7134956/nand_programmer/firmware/programmer/cdc.c

/*  Copyright (C) 2020 NANDO authors
 *  This program is free software; you can redistribute it and/or modify
 *  it under the terms of the GNU General Public License version 3.
 */

#include "ch32v30x.h"
#include "nand_programmer.h"

#define SEND_TIMEOUT 0x1000000
#include "usbd_core.h"
#include "usbd_cdc.h"

/*!< endpoint address */
#define CDC_IN_EP  0x81
#define CDC_OUT_EP 0x02
#define CDC_INT_EP 0x83

#define USBD_VID           0xFFFF
#define USBD_PID           0xFFFF
#define USBD_MAX_POWER     100
#define USBD_LANGID_STRING 1033

/*!< config descriptor size */
#define USB_CONFIG_SIZE (9 + CDC_ACM_DESCRIPTOR_LEN)

/*!< global descriptor */
static const uint8_t cdc_descriptor[] = {
    USB_DEVICE_DESCRIPTOR_INIT(USB_2_0, 0xEF, 0x02, 0x01, USBD_VID, USBD_PID, 0x0100, 0x01),
    USB_CONFIG_DESCRIPTOR_INIT(USB_CONFIG_SIZE, 0x02, 0x01, USB_CONFIG_BUS_POWERED, USBD_MAX_POWER),
    CDC_ACM_DESCRIPTOR_INIT(0x00, CDC_INT_EP, CDC_OUT_EP, CDC_IN_EP, 0x02),
    ///////////////////////////////////////
    /// string0 descriptor
    ///////////////////////////////////////
    USB_LANGID_INIT(USBD_LANGID_STRING),
    ///////////////////////////////////////
    /// string1 descriptor
    ///////////////////////////////////////
    0x14,                       /* bLength */
    USB_DESCRIPTOR_TYPE_STRING, /* bDescriptorType */
    'C', 0x00,                  /* wcChar0 */
    'h', 0x00,                  /* wcChar1 */
    'e', 0x00,                  /* wcChar2 */
    'r', 0x00,                  /* wcChar3 */
    'r', 0x00,                  /* wcChar4 */
    'y', 0x00,                  /* wcChar5 */
    'U', 0x00,                  /* wcChar6 */
    'S', 0x00,                  /* wcChar7 */
    'B', 0x00,                  /* wcChar8 */
    ///////////////////////////////////////
    /// string2 descriptor
    ///////////////////////////////////////
    0x26,                       /* bLength */
    USB_DESCRIPTOR_TYPE_STRING, /* bDescriptorType */
    'C', 0x00,                  /* wcChar0 */
    'h', 0x00,                  /* wcChar1 */
    'e', 0x00,                  /* wcChar2 */
    'r', 0x00,                  /* wcChar3 */
    'r', 0x00,                  /* wcChar4 */
    'y', 0x00,                  /* wcChar5 */
    'U', 0x00,                  /* wcChar6 */
    'S', 0x00,                  /* wcChar7 */
    'B', 0x00,                  /* wcChar8 */
    ' ', 0x00,                  /* wcChar9 */
    'C', 0x00,                  /* wcChar10 */
    'D', 0x00,                  /* wcChar11 */
    'C', 0x00,                  /* wcChar12 */
    ' ', 0x00,                  /* wcChar13 */
    'D', 0x00,                  /* wcChar14 */
    'E', 0x00,                  /* wcChar15 */
    'M', 0x00,                  /* wcChar16 */
    'O', 0x00,                  /* wcChar17 */
    ///////////////////////////////////////
    /// string3 descriptor
    ///////////////////////////////////////
    0x16,                       /* bLength */
    USB_DESCRIPTOR_TYPE_STRING, /* bDescriptorType */
    '2', 0x00,                  /* wcChar0 */
    '0', 0x00,                  /* wcChar1 */
    '2', 0x00,                  /* wcChar2 */
    '2', 0x00,                  /* wcChar3 */
    '1', 0x00,                  /* wcChar4 */
    '2', 0x00,                  /* wcChar5 */
    '3', 0x00,                  /* wcChar6 */
    '4', 0x00,                  /* wcChar7 */
    '5', 0x00,                  /* wcChar8 */
    '6', 0x00,                  /* wcChar9 */
#ifdef CONFIG_USB_HS
    ///////////////////////////////////////
    /// device qualifier descriptor
    ///////////////////////////////////////
    0x0a,
    USB_DESCRIPTOR_TYPE_DEVICE_QUALIFIER,
    0x00,
    0x02,
    0x02,
    0x02,
    0x01,
    0x40,
    0x01,
    0x00,
#endif
    0x00
};

#ifdef CONFIG_USB_HS
#define CDC_MAX_MPS 512
#else
#define CDC_MAX_MPS 64
#endif

uint8_t rx_data[CDC_MAX_MPS];
uint8_t tx_data[CDC_MAX_MPS];
volatile uint32_t len_data = 0;
volatile bool tx_busy = false;

void usbd_configure_done_callback(void)
{
    usbd_ep_start_read(CDC_OUT_EP, rx_data, CDC_MAX_MPS);
}

void usbd_cdc_acm_bulk_out(uint8_t ep, uint32_t nbytes)
{
    len_data = nbytes;
}

void usbd_cdc_acm_bulk_in(uint8_t ep, uint32_t nbytes)
{
    tx_busy = false;
}

/*!< endpoint call back */
struct usbd_endpoint cdc_out_ep = {
    .ep_addr = CDC_OUT_EP,
    .ep_cb = usbd_cdc_acm_bulk_out
};

struct usbd_endpoint cdc_in_ep = {
    .ep_addr = CDC_IN_EP,
    .ep_cb = usbd_cdc_acm_bulk_in
};

struct usbd_interface intf0;
struct usbd_interface intf1;

void cdc_acm_init(void)
{
    usbd_desc_register(cdc_descriptor);
    usbd_add_interface(usbd_cdc_acm_init_intf(&intf0));
    usbd_add_interface(usbd_cdc_acm_init_intf(&intf1));
    usbd_add_endpoint(&cdc_out_ep);
    usbd_add_endpoint(&cdc_in_ep);
    usbd_initialize();
}

volatile uint8_t dtr_enable = 0;

void usbd_cdc_acm_set_dtr(uint8_t intf, bool dtr)
{
    if (dtr) {
        dtr_enable = 1;
    } else {
        dtr_enable = 0;
    }
}

static int cdc_send(uint8_t *data, uint32_t len)
{
    while(tx_busy){};
    tx_busy = true;
    memcpy(tx_data, data, len);
    usbd_ep_start_write(CDC_IN_EP, tx_data, len);
    return 0;
}

static uint32_t cdc_peek(uint8_t **data)
{
    *data = rx_data;
    return len_data;
}

static void cdc_consume()
{
    len_data = 0;
    usbd_ep_start_read(CDC_OUT_EP, rx_data, CDC_MAX_MPS);
}

static np_comm_cb_t cdc_comm_cb =
{
    .send = cdc_send,
    .peek = cdc_peek,
    .consume = cdc_consume,
};

void cdc_init()
{
    extern void cdc_acm_init(void);
    cdc_acm_init();
    while (!usb_device_is_configured()) {}
    np_comm_register(&cdc_comm_cb);
}

void usb_dc_low_level_init(void)
{
    RCC_USBCLK48MConfig(RCC_USBCLK48MCLKSource_USBPHY);
    RCC_USBHSPLLCLKConfig(RCC_HSBHSPLLCLKSource_HSE);
    RCC_USBHSConfig(RCC_USBPLL_Div2);
    RCC_USBHSPLLCKREFCLKConfig(RCC_USBHSPLLCKREFCLK_4M);
    RCC_USBHSPHYPLLALIVEcmd(ENABLE);
    RCC_AHBPeriphClockCmd(RCC_AHBPeriph_USBHS, ENABLE);
    NVIC_EnableIRQ(USBHS_IRQn);
}
